Photonsters/ESParaSite/include/ESP32.h

// ESP32.h

/* ESParaSite-ESP32 Data Logger
        Authors: Andy (SolidSt8Dad) Eakin

        Please see /ATTRIB for full credits and OSS License Info
        Please see /LIBRARIES for necessary libraries
        Please see /VERSION for Hstory

        All Derived Content is subject to the most restrictive licence of it's
        source.

        All Original content is free and unencumbered software released into the
        public domain.

        The Author(s) are extremely grateful for the amazing open source
        communities that work to support all of the sensors, microcontrollers,
        web standards, etc.
*/

#define LED_BUILTIN 2
#define LED_ON HIGH
#define LED_OFF LOW

// See file
// .../hardware/espressif/esp32/variants/(esp32|doitESP32devkitV1)/pins_arduino.h
#define LED_BUILTIN                                                            \
  2 // Pin D2 mapped to pin GPIO2/ADC12 of ESP32, control on-board LED
#define PIN_LED                                                                \
  2 // Pin D2 mapped to pin GPIO2/ADC12 of ESP32, control on-board LED

#define PIN_D0 0 // Pin D0 mapped to pin GPIO0/BOOT/ADC11/TOUCH1 of ESP32
#define PIN_D1 1 // Pin D1 mapped to pin GPIO1/TX0 of ESP32
#define PIN_D2 2 // Pin D2 mapped to pin GPIO2/ADC12/TOUCH2 of ESP32
#define PIN_D3 3 // Pin D3 mapped to pin GPIO3/RX0 of ESP32
#define PIN_D4 4 // Pin D4 mapped to pin GPIO4/ADC10/TOUCH0 of ESP32
#define PIN_D5 5 // Pin D5 mapped to pin GPIO5/SPISS/VSPI_SS of ESP32
#define PIN_D6 6 // Pin D6 mapped to pin GPIO6/FLASH_SCK of ESP32
#define PIN_D7 7 // Pin D7 mapped to pin GPIO7/FLASH_D0 of ESP32
#define PIN_D8 8 // Pin D8 mapped to pin GPIO8/FLASH_D1 of ESP32
#define PIN_D9 9 // Pin D9 mapped to pin GPIO9/FLASH_D2 of ESP32

#define PIN_D10 10 // Pin D10 mapped to pin GPIO10/FLASH_D3 of ESP32
#define PIN_D11 11 // Pin D11 mapped to pin GPIO11/FLASH_CMD of ESP32
#define PIN_D12                                                                \
  12 // Pin D12 mapped to pin GPIO12/HSPI_MISO/ADC15/TOUCH5/TDI of ESP32
#define PIN_D13                                                                \
  13 // Pin D13 mapped to pin GPIO13/HSPI_MOSI/ADC14/TOUCH4/TCK of ESP32
#define PIN_D14                                                                \
  14 // Pin D14 mapped to pin GPIO14/HSPI_SCK/ADC16/TOUCH6/TMS of ESP32
#define PIN_D15                                                                \
  15 // Pin D15 mapped to pin GPIO15/HSPI_SS/ADC13/TOUCH3/TDO of ESP32
#define PIN_D16 16 // Pin D16 mapped to pin GPIO16/TX2 of ESP32
#define PIN_D17 17 // Pin D17 mapped to pin GPIO17/RX2 of ESP32
#define PIN_D18 18 // Pin D18 mapped to pin GPIO18/VSPI_SCK of ESP32
#define PIN_D19 19 // Pin D19 mapped to pin GPIO19/VSPI_MISO of ESP32

#define PIN_D21 21 // Pin D21 mapped to pin GPIO21/SDA of ESP32
#define PIN_D22 22 // Pin D22 mapped to pin GPIO22/SCL of ESP32
#define PIN_D23 23 // Pin D23 mapped to pin GPIO23/VSPI_MOSI of ESP32
#define PIN_D24 24 // Pin D24 mapped to pin GPIO24 of ESP32
#define PIN_D25 25 // Pin D25 mapped to pin GPIO25/ADC18/DAC1 of ESP32
#define PIN_D26 26 // Pin D26 mapped to pin GPIO26/ADC19/DAC2 of ESP32
#define PIN_D27 27 // Pin D27 mapped to pin GPIO27/ADC17/TOUCH7 of ESP32

#define PIN_D32 32 // Pin D32 mapped to pin GPIO32/ADC4/TOUCH9 of ESP32
#define PIN_D33 33 // Pin D33 mapped to pin GPIO33/ADC5/TOUCH8 of ESP32
#define PIN_D34 34 // Pin D34 mapped to pin GPIO34/ADC6 of ESP32

// Only GPIO pin < 34 can be used as output. Pins >= 34 can be only inputs
// See .../cores/esp32/esp32-hal-gpio.h/c
//#define digitalPinIsValid(pin)          ((pin) < 40 &&
// esp32_gpioMux[(pin)].reg) #define digitalPinCanOutput(pin)        ((pin) < 34
//&& esp32_gpioMux[(pin)].reg) #define digitalPinToRtcPin(pin)         (((pin) <
// 40)?esp32_gpioMux[(pin)].rtc:-1) #define digitalPinToAnalogChannel(pin)
//(((pin) < 40)?esp32_gpioMux[(pin)].adc:-1) #define
// digitalPinToTouchChannel(pin)   (((pin) < 40)?esp32_gpioMux[(pin)].touch:-1)
//#define digitalPinToDacChannel(pin)     (((pin) == 25)?0:((pin) == 26)?1:-1)

#define PIN_D35 35 // Pin D35 mapped to pin GPIO35/ADC7 of ESP32
#define PIN_D36 36 // Pin D36 mapped to pin GPIO36/ADC0/SVP of ESP32
#define PIN_D39 39 // Pin D39 mapped to pin GPIO39/ADC3/SVN of ESP32

#define PIN_RX0 3 // Pin RX0 mapped to pin GPIO3/RX0 of ESP32
#define PIN_TX0 1 // Pin TX0 mapped to pin GPIO1/TX0 of ESP32

#define PIN_SCL 22 // Pin SCL mapped to pin GPIO22/SCL of ESP32
#define PIN_SDA 21 // Pin SDA mapped to pin GPIO21/SDA of ESP32
