Photonsters/ESParaSite/include/ESParaSite_DebugUtils.h

/*
DebugUtils.h - Simple debugging utilities.
Copyright (C) 2011 Fabio Varesano <fabio at varesano dot net>

Ideas taken from:
http://www.arduino.cc/cgi-bin/yabb2/YaBB.pl?num=1271517197

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
*/

#ifndef DEBUGUTILS_H
#define DEBUGUTILS_H

// DEBUG_L1 dumps verbose data about what the program is doing
//#define DEBUG_L1

// DEBUG_L2 dumps sensor data on every read as well as EEPROM values and some
// variables.  Additionally several 500ms Delays are added which will slow down the web server response.
//#define DEBUG_L2

// DEBUG_L3 dumps time data on every loop this can cause some terminals to crash
// and should not be used with VSCode as your terminal.
//#define DEBUG_L3

#endif
